pilotak/eth-io/images/assembly/1.jpg

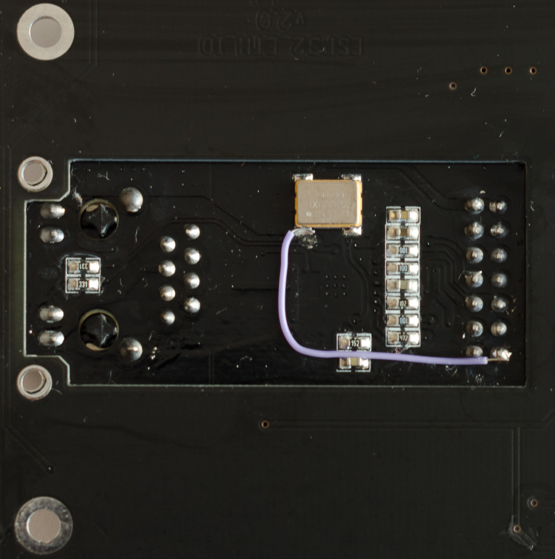
images/assembly/1.jpg
