pilotak/eth-io/images/assembly/8.jpg

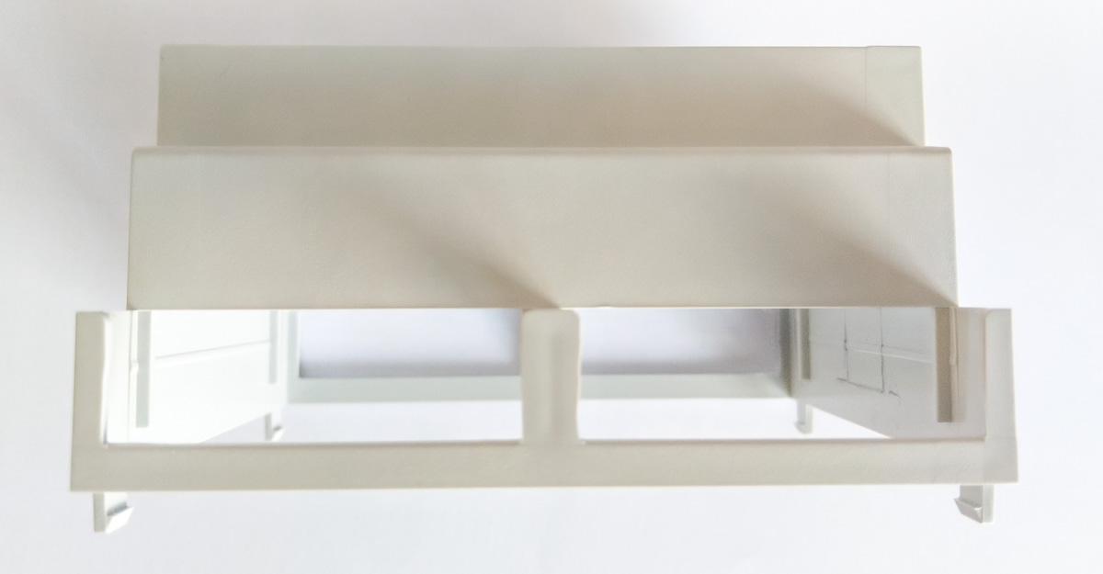
images/assembly/8.jpg
