pilotak/eth-io/images/assembly/9.jpg

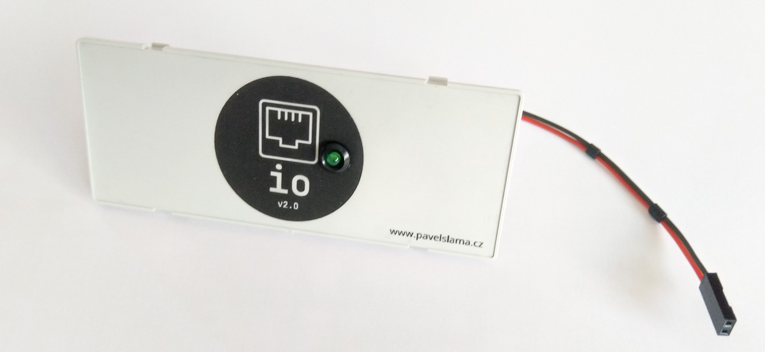
images/assembly/9.jpg
