pilotak/eth-io/images/assembly/10.jpg

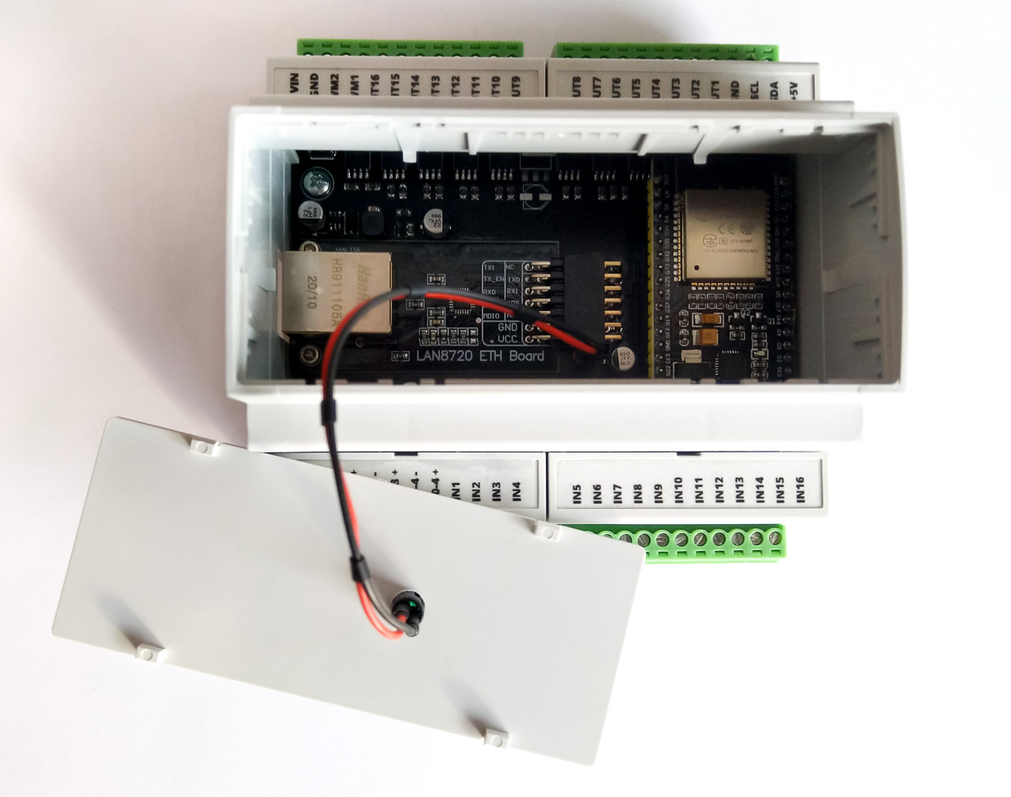
images/assembly/10.jpg
